yamamo2shun1/PrM/pdf/Selector_Gain_brd.pdf

+15V

Phono(L) | -15V

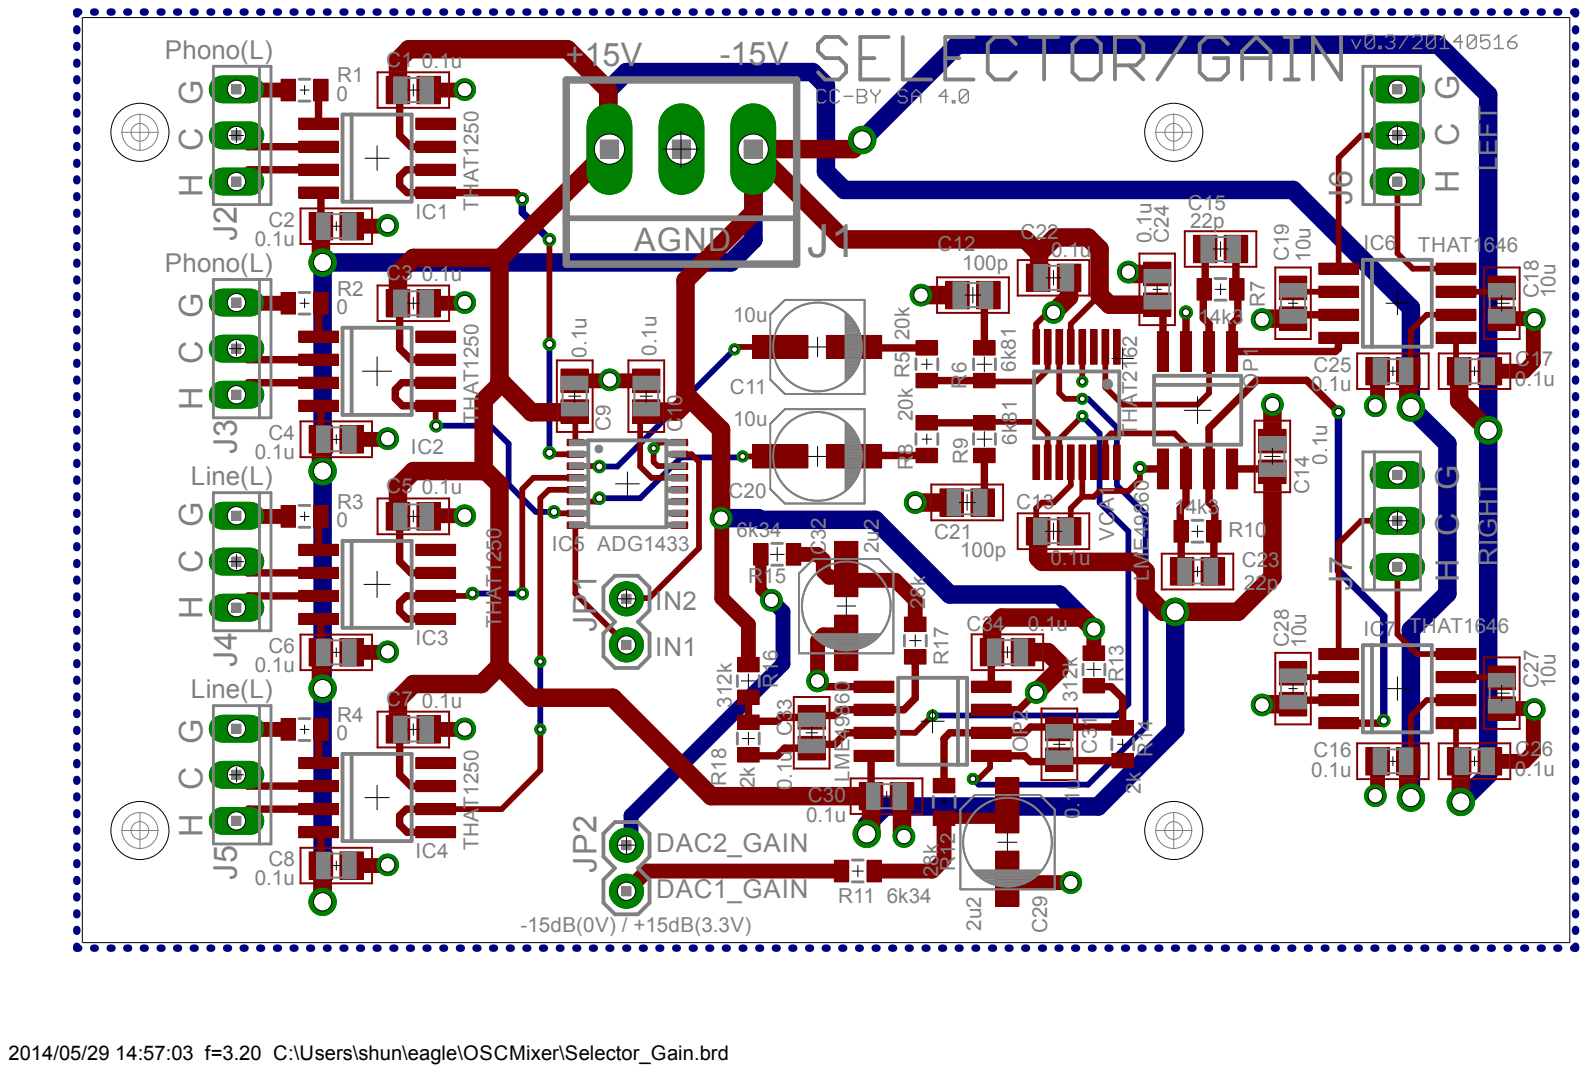
[picture p4: page 1]

2014/05/29 14:57:03 f=3.20 C:\Users\shun\eagle\OSCMixer\Selector_Gain.brd
