yamamo2shun1/PrM/pdf/RCA_sch.pdf

A

A

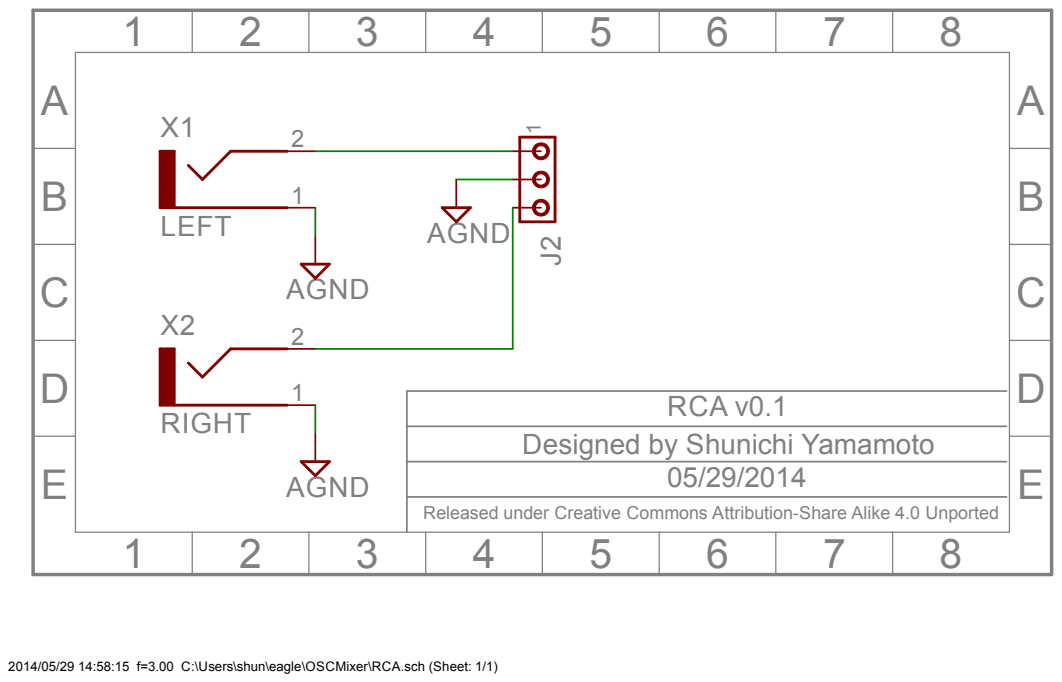
[picture p14: page 1]
RCA v0.1; AGND; LEFT; RIGHT

Designed by Shunichi Yamamoto

Released under Creative Commons Attribution-Share Alike 4.0 Unported

2014/05/29 14:58:15 f=3.00 C:\Users\shun\eagle\OSCMixer\RCA.sch (Sheet: 1/1)
