yamamo2shun1/PrM/pdf/Selector_Gain_sch0.pdf

A

A

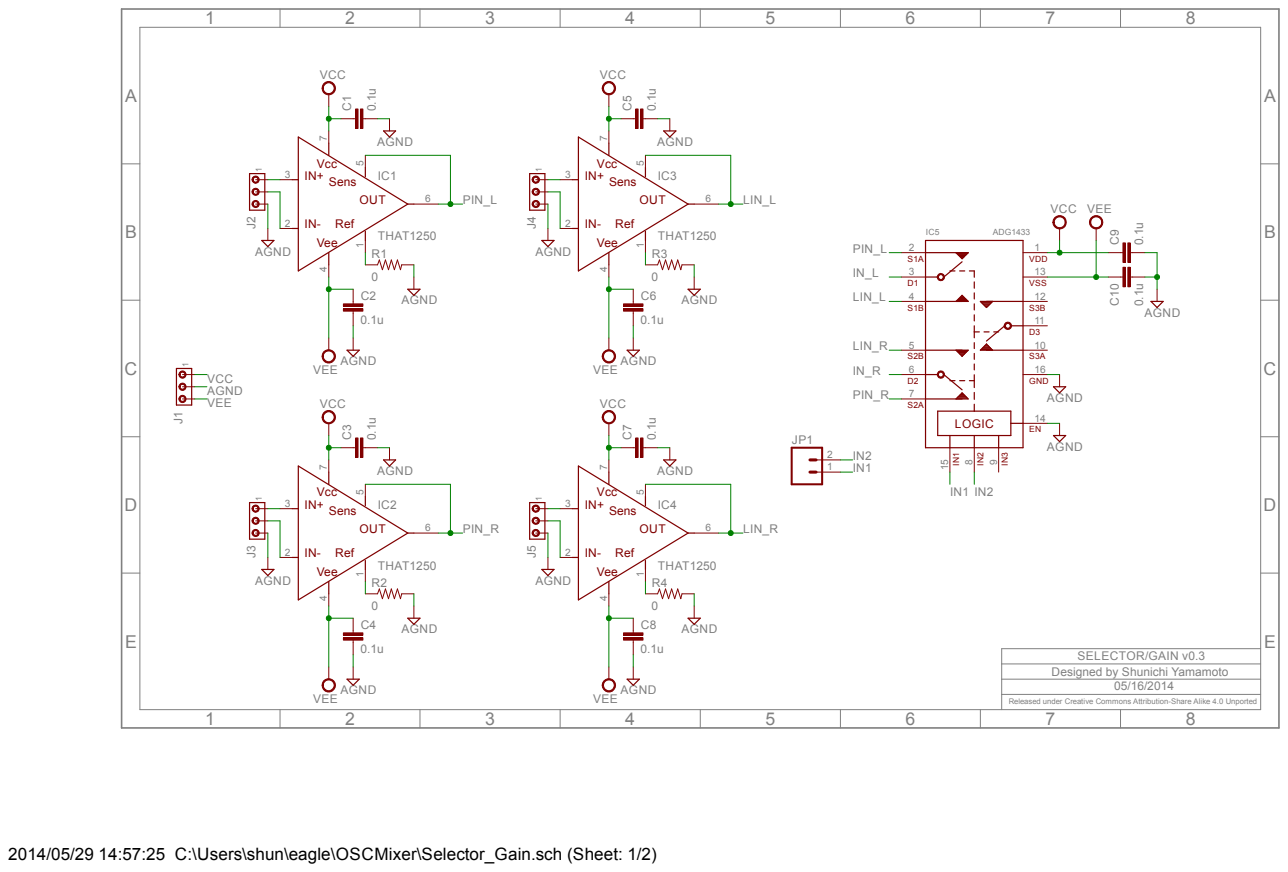
[picture p15: page 1]

SELECTOR/GAIN v0.3
Designed by Shunichi Yamamoto

Released under Creative Commons Attribution-Share Alike 4.0 Unported

2014/05/29 14:57:25 C:\Users\shun\eagle\OSCMixer\Selector_Gain.sch (Sheet: 1/2)
