yamamo2shun1/PrM/pdf/Selector_Gain_sch1.pdf

A

A

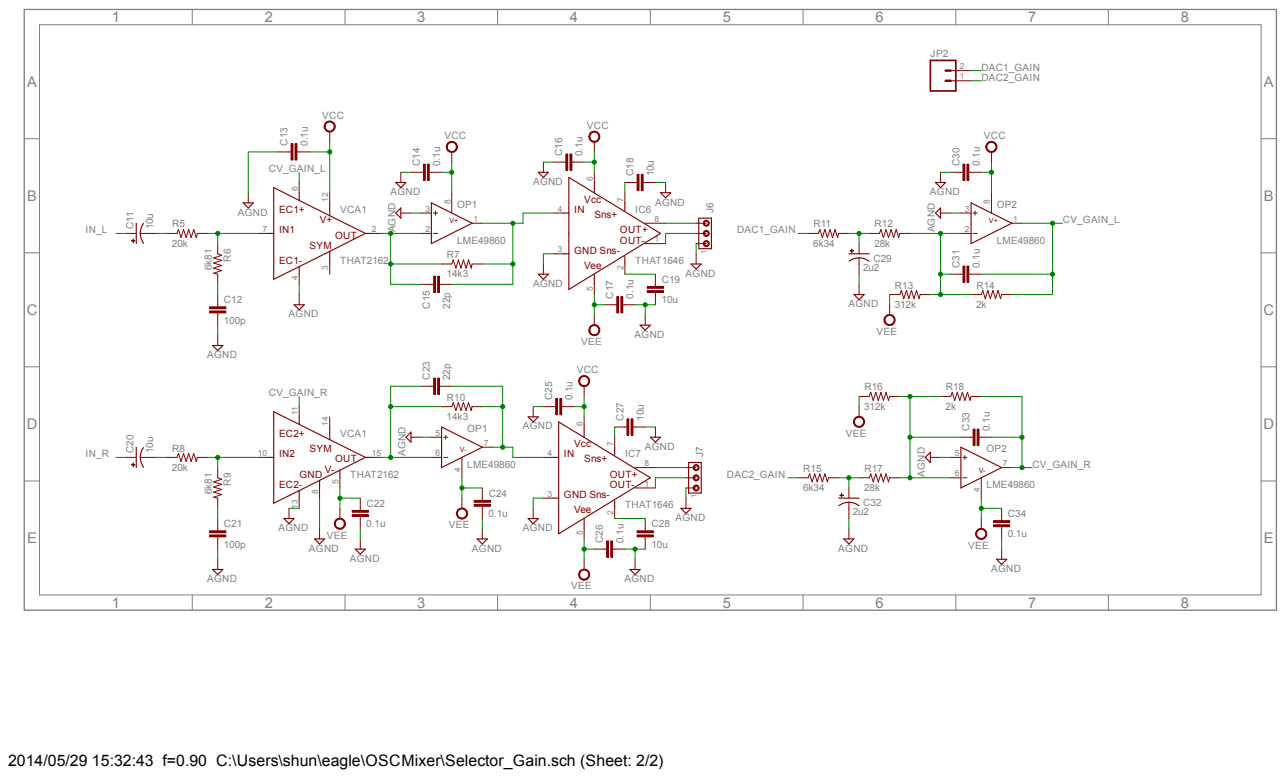
[picture p16: page 1]

2014/05/29 15:32:43 f=0.90 C:\Users\shun\eagle\OSCMixer\Selector_Gain.sch (Sheet: 2/2)
