yamamo2shun1/PrM/pdf/Summing_brd.pdf

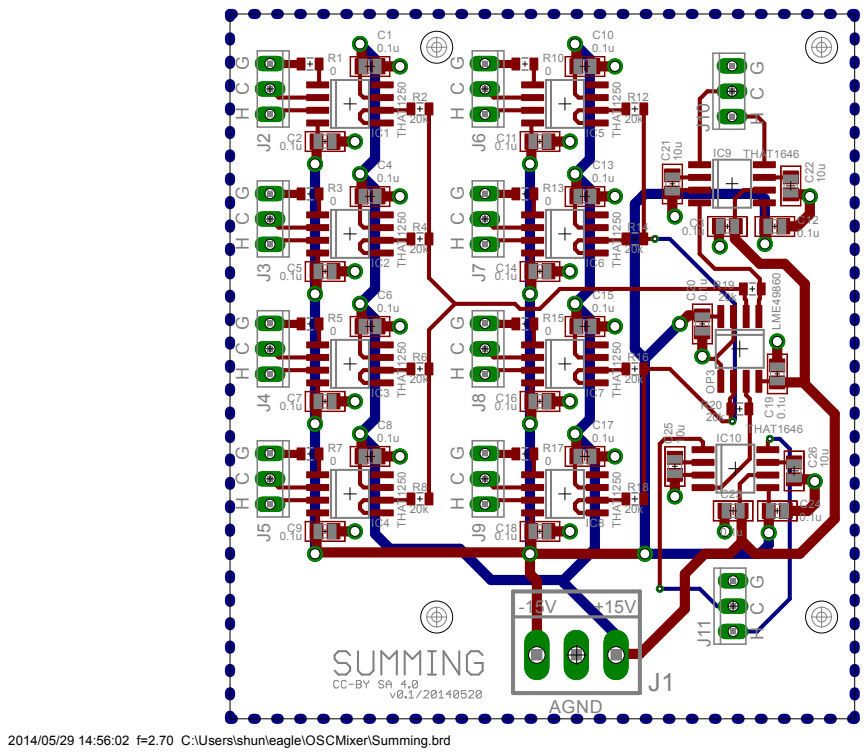
[picture p17: page 1]

2014/05/29 14:56:02 f=2.70 C:\Users\shun\eagle\OSCMixer\Summing.brd
