yamamo2shun1/PrM/pdf/Summing_sch.pdf

A

A

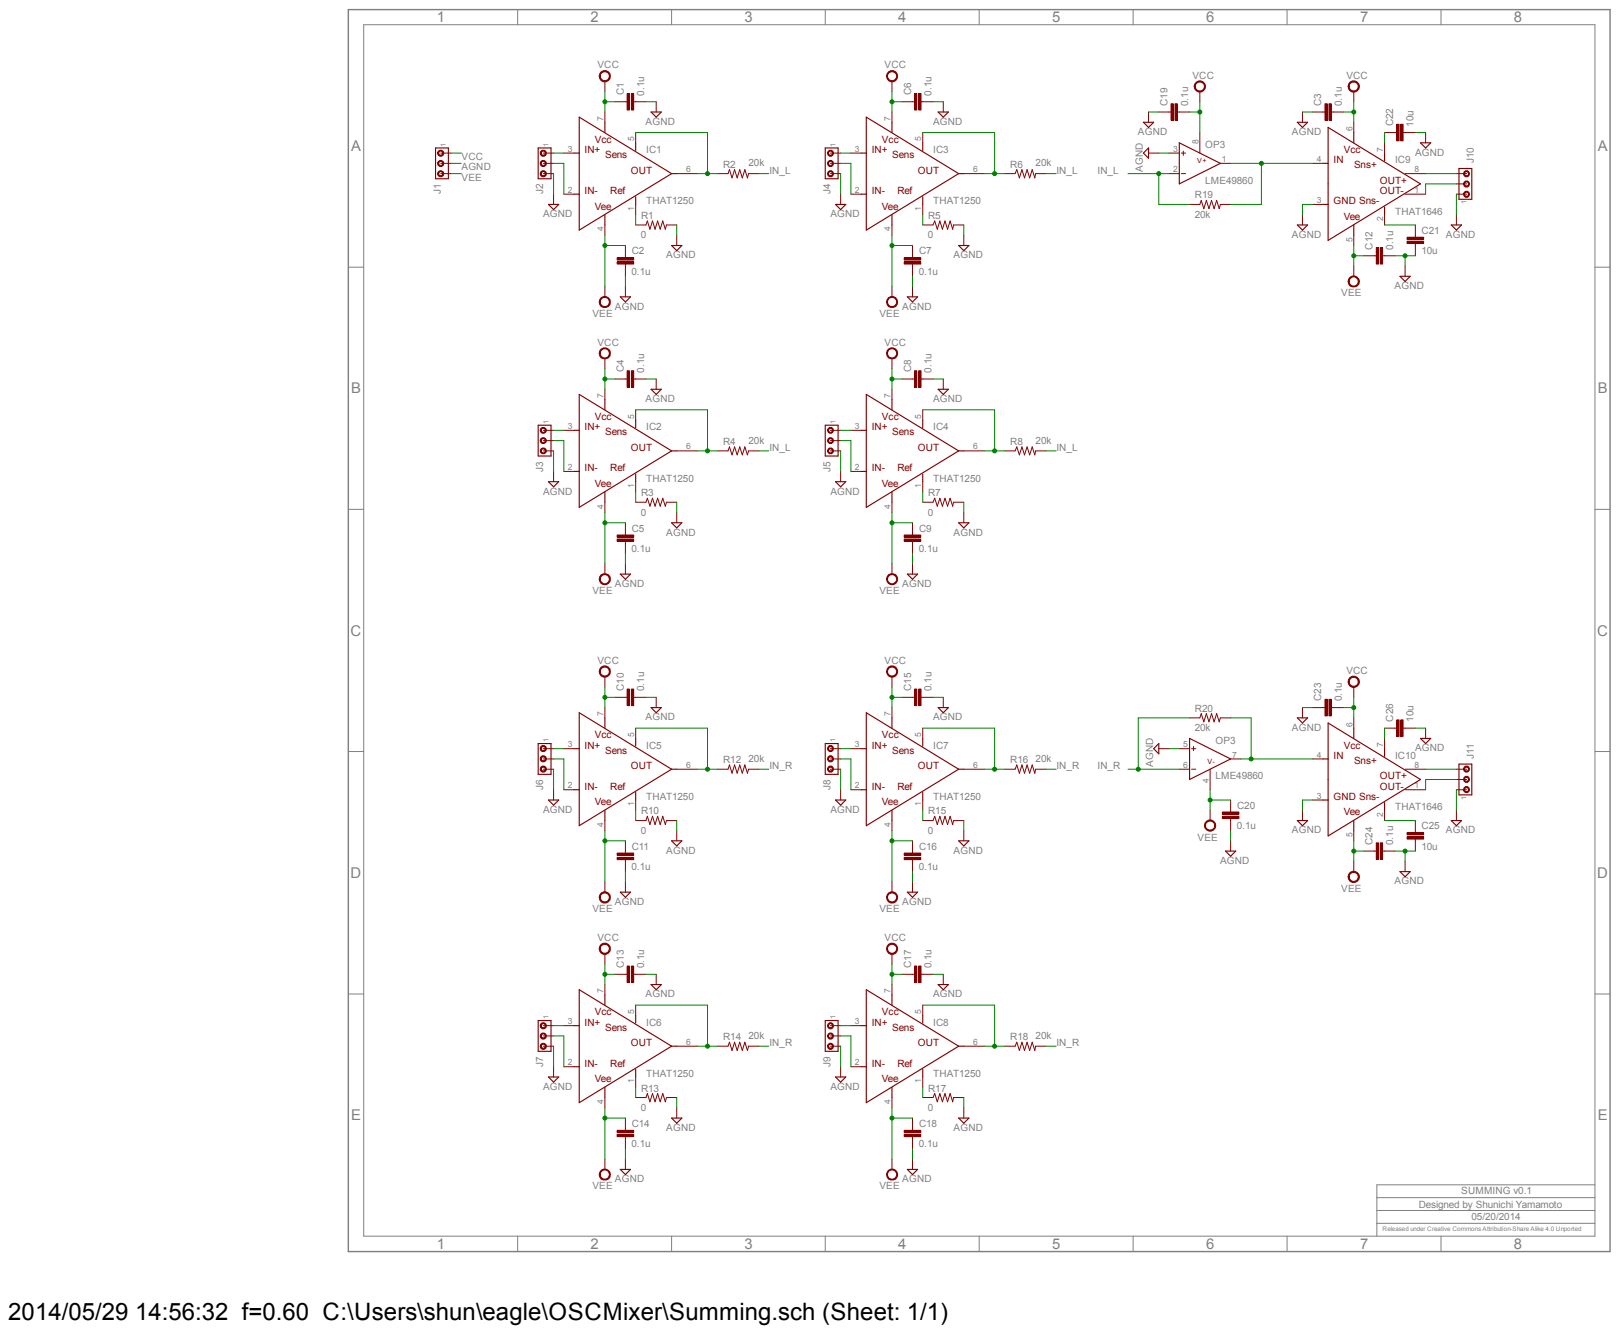
[picture p18: page 1]

Designed by Shunichi Yamamoto

Released under Creative Commons Attribution-Share Alike 4.0 Unported

2014/05/29 14:56:32 f=0.60 C:\Users\shun\eagle\OSCMixer\Summing.sch (Sheet: 1/1)
