yamamo2shun1/PrM/pdf/TRS_brd.pdf

X1

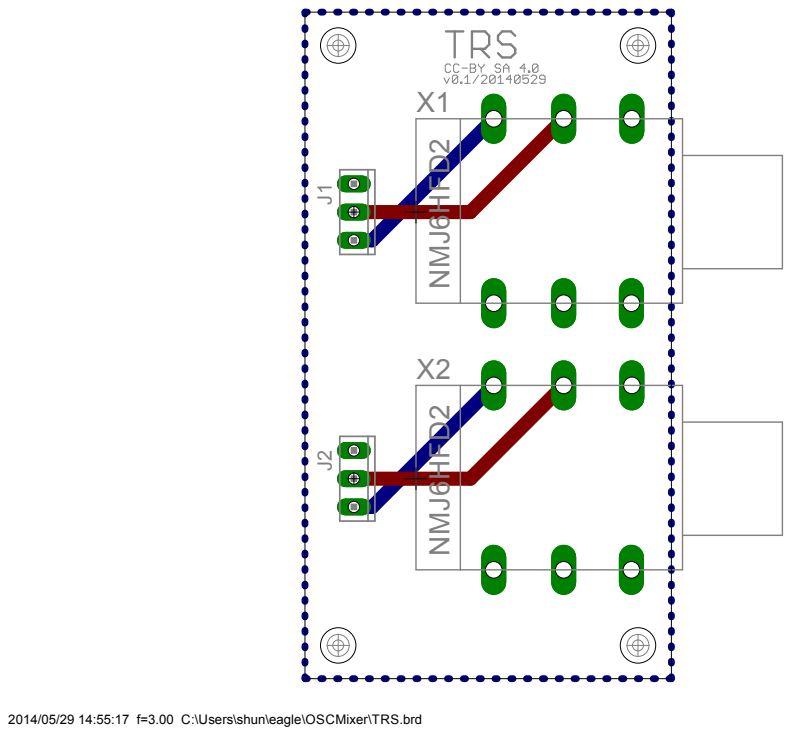
[picture p19: page 1]

2014/05/29 14:55:17 f=3.00 C:\Users\shun\eagle\OSCMixer\TRS.brd
