yamamo2shun1/PrM/pdf/TRS_sch.pdf

A

A

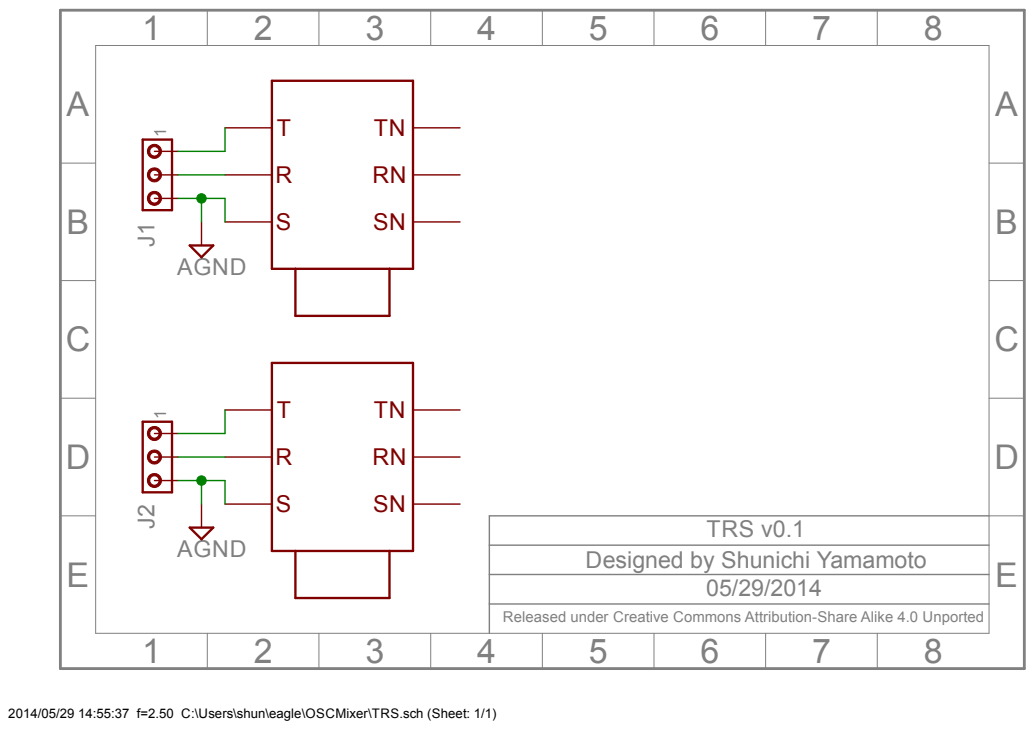
[picture p20: page 1]
TRS v0.1; AGND

Designed by Shunichi Yamamoto

Released under Creative Commons Attribution-Share Alike 4.0 Unported

2014/05/29 14:55:37 f=2.50 C:\Users\shun\eagle\OSCMixer\TRS.sch (Sheet: 1/1)
