yamamo2shun1/PrM/pdf/Volume_brd.pdf

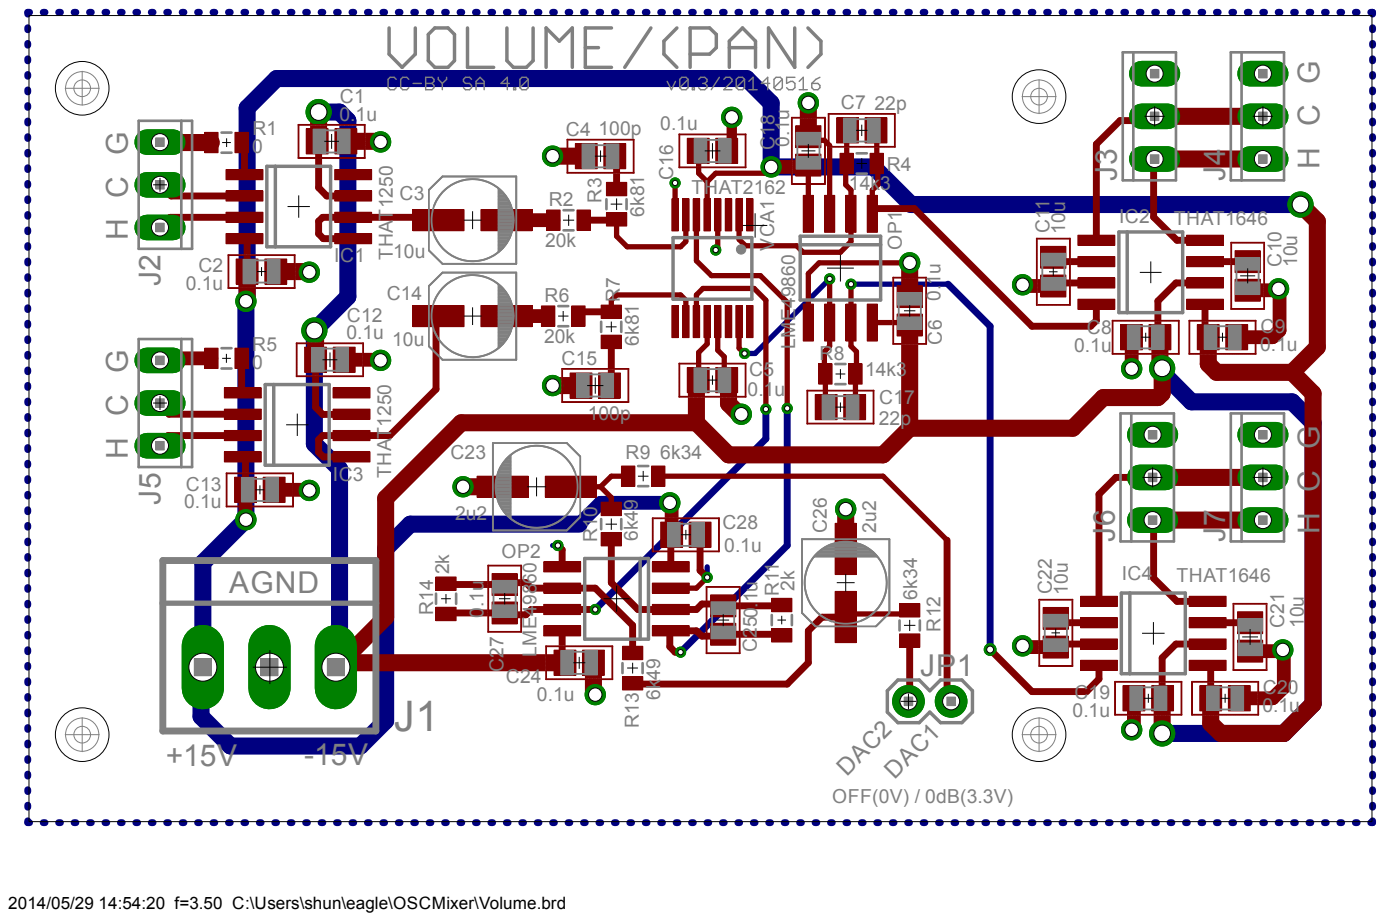
[picture p21: page 1]

2014/05/29 14:54:20 f=3.50 C:\Users\shun\eagle\OSCMixer\Volume.brd
