yamamo2shun1/PrM/pdf/Volume_sch.pdf

1 | 2 | 3 | 4 | 5 | 6 | 7 | 8

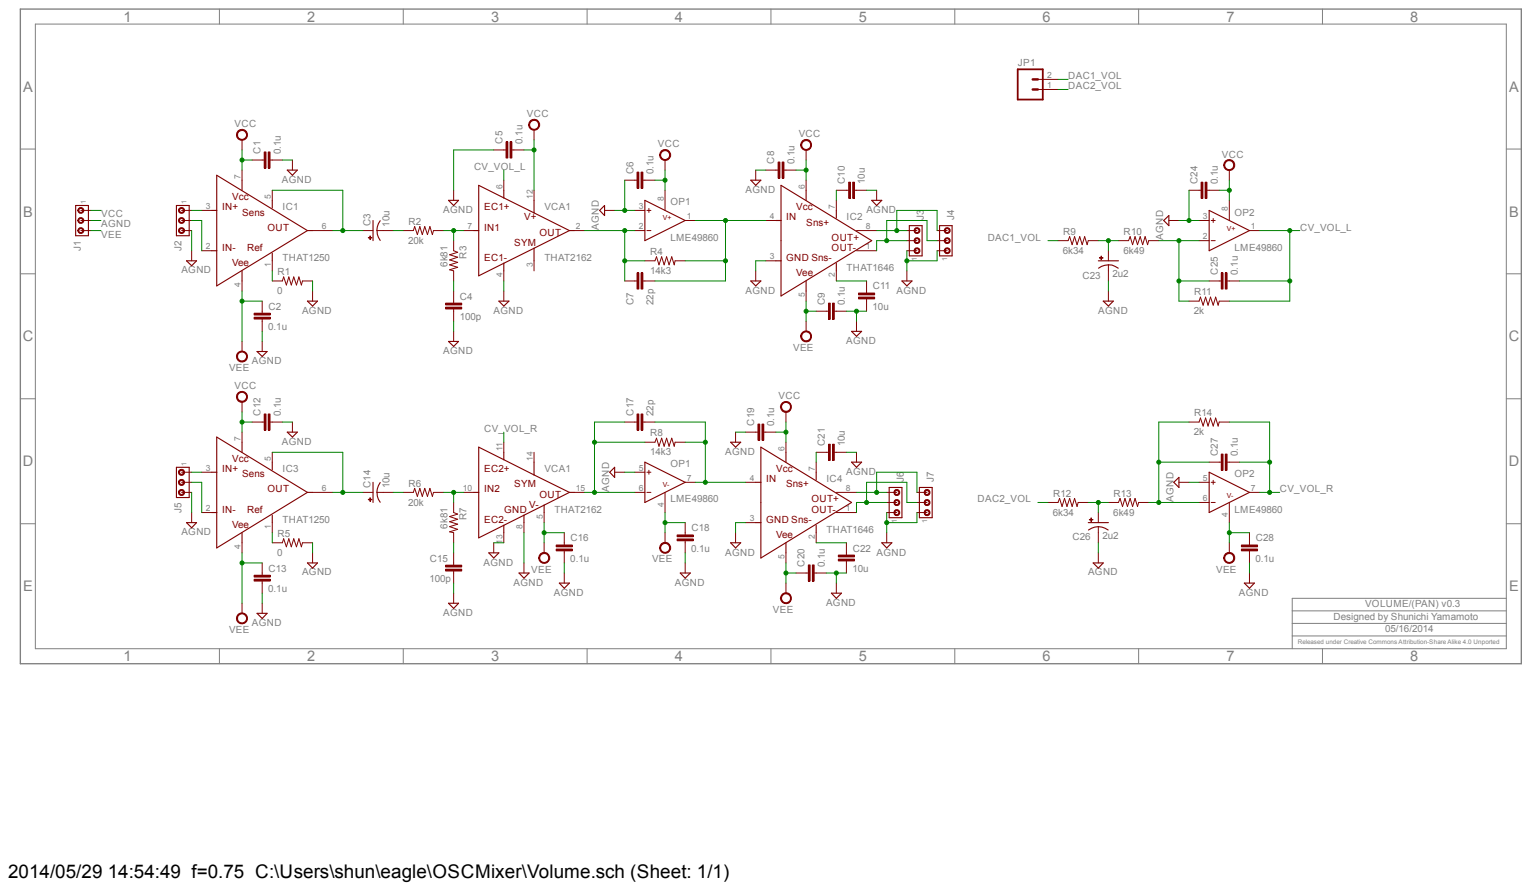
[picture p22: page 1]

VOLUME/(PAN) v0.3
Designed by Shunichi Yamamoto

Released under Creative Commons Attribution-Share Alike 4.0 Unported

2014/05/29 14:54:49 f=0.75 C:\Users\shun\eagle\OSCMixer\Volume.sch (Sheet: 1/1)
