yamamo2shun1/PrM/pdf/XFader_Assign_brd.pdf

J

P

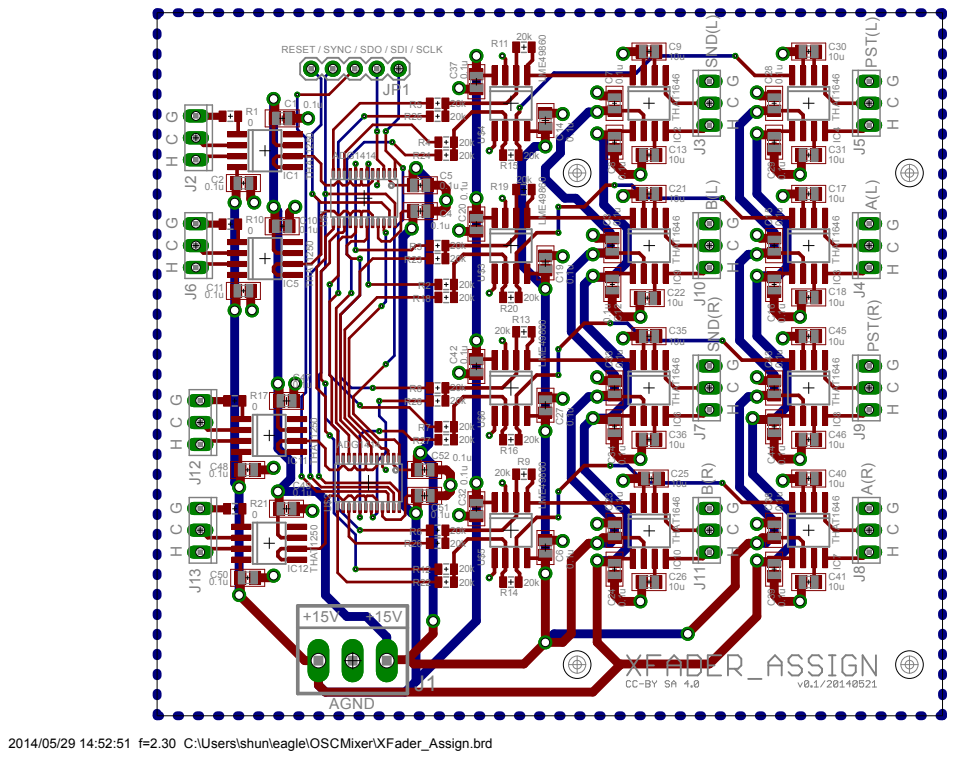
[picture p23: page 1]

R 2
R 1 8

R 8
R 2 8
