yamamo2shun1/PrM/pdf/XFader_Assign_sch.pdf

A

A

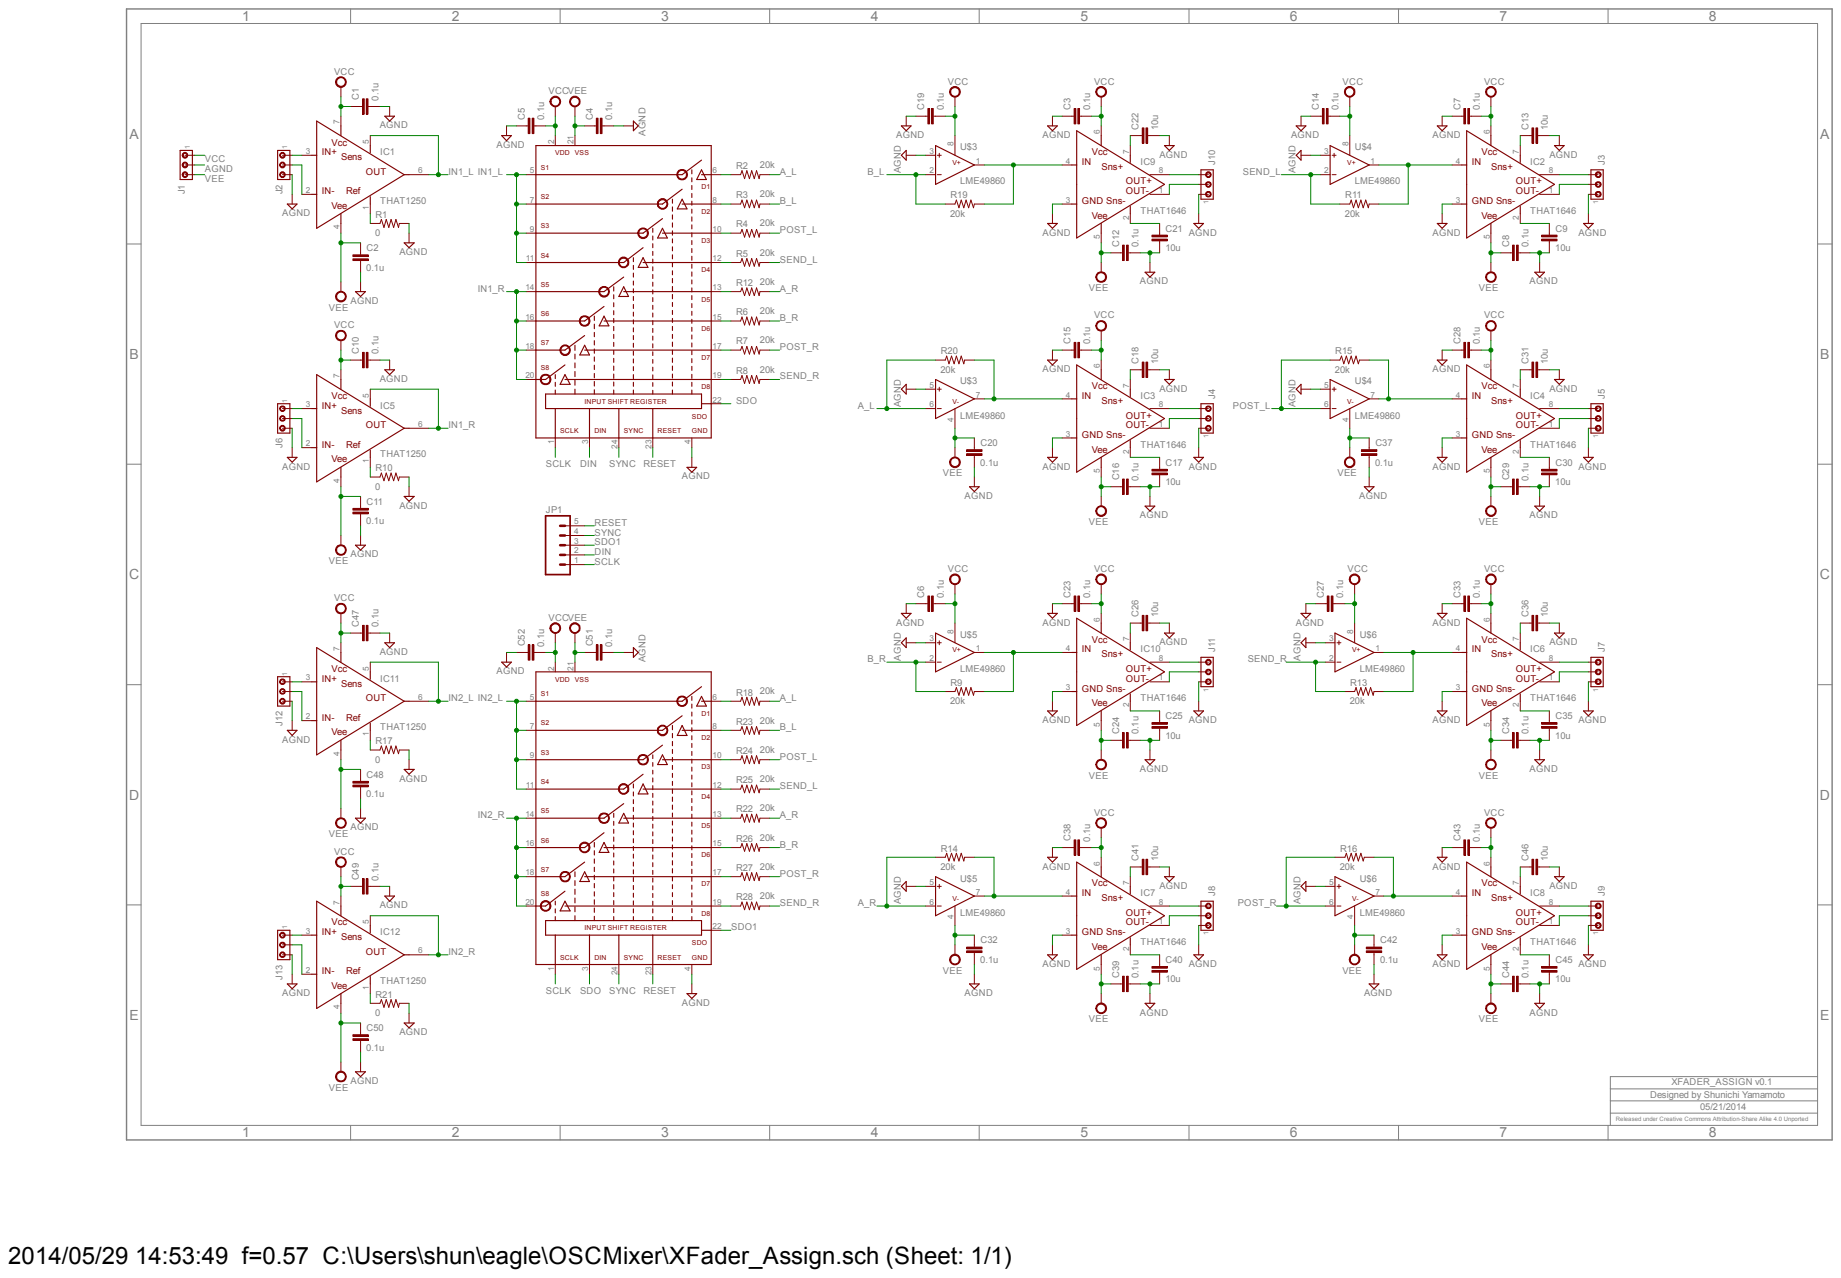
[picture p24: page 1]

VCC | | VCC | VCC

XFADER_ASSIGN v0.1
Designed by Shunichi Yamamoto

Released under Creative Commons Attribution-Share Alike 4.0 Unported

2014/05/29 14:53:49 f=0.57 C:\Users\shun\eagle\OSCMixer\XFader_Assign.sch (Sheet: 1/1)
