yamamo2shun1/PrM/pdf/XLR_brd.pdf

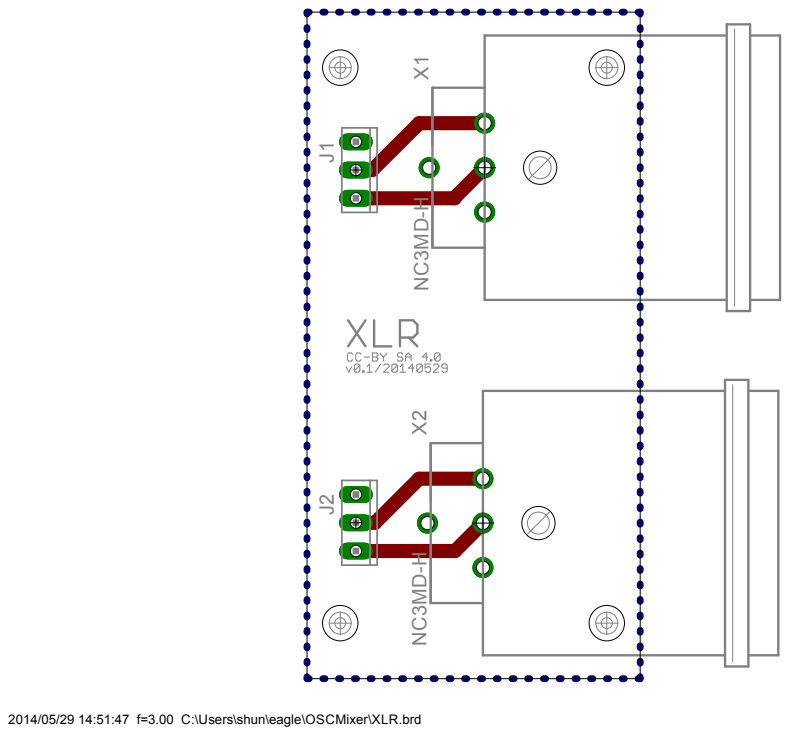
[picture p25: page 1]

2014/05/29 14:51:47 f=3.00 C:\Users\shun\eagle\OSCMixer\XLR.brd
