yamamo2shun1/PrM/pdf/XLR_sch.pdf

A

A

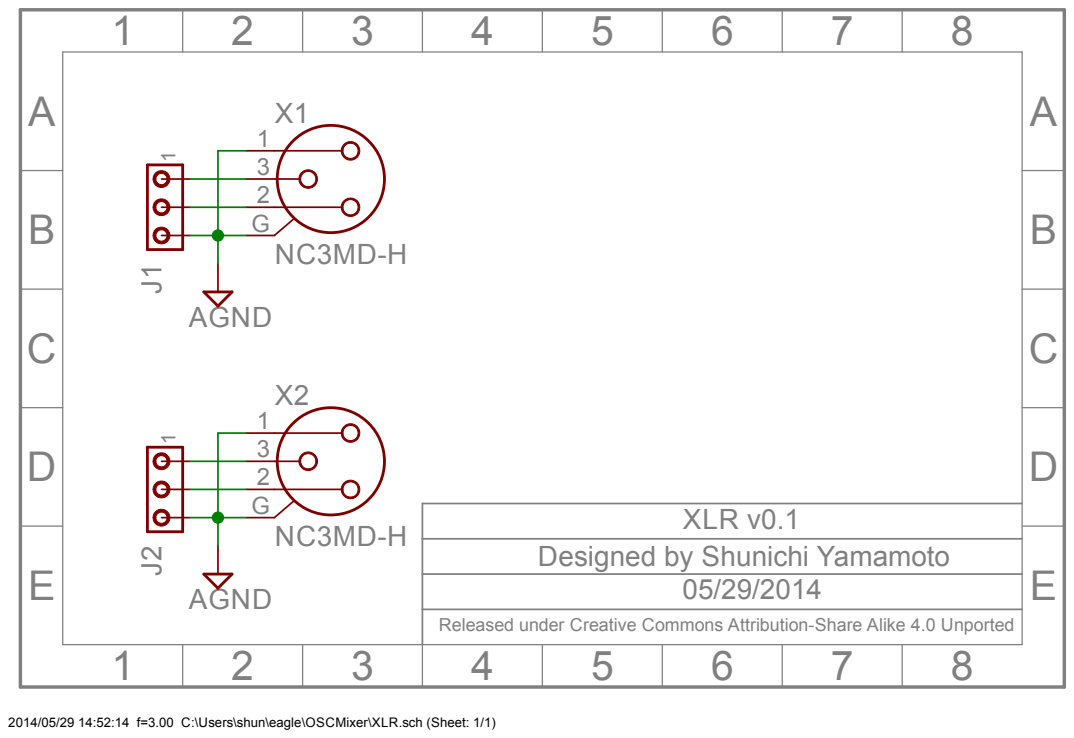
[picture p26: page 1]
XLR v0.1; AGND

Designed by Shunichi Yamamoto

Released under Creative Commons Attribution-Share Alike 4.0 Unported

2014/05/29 14:52:14 f=3.00 C:\Users\shun\eagle\OSCMixer\XLR.sch (Sheet: 1/1)
